justinmklam/iot-sourdough-starter-monitor/iot-sourdough/include/display.h

#pragma once

void initializeDisplay();
void tDisplayCallback();
void setNextDisplayState();

enum DisplayStates {
    DISPLAY_STATE_DEFAULT,
    DISPLAY_STATE_GRAPH,
    DISPLAY_STATE_ADVANCED,
    NUM_DISPLAY_STATES
};
